ExpressLRS/Handset/Wiki/Filter Boards/20210325_175824414_iOS.jpg

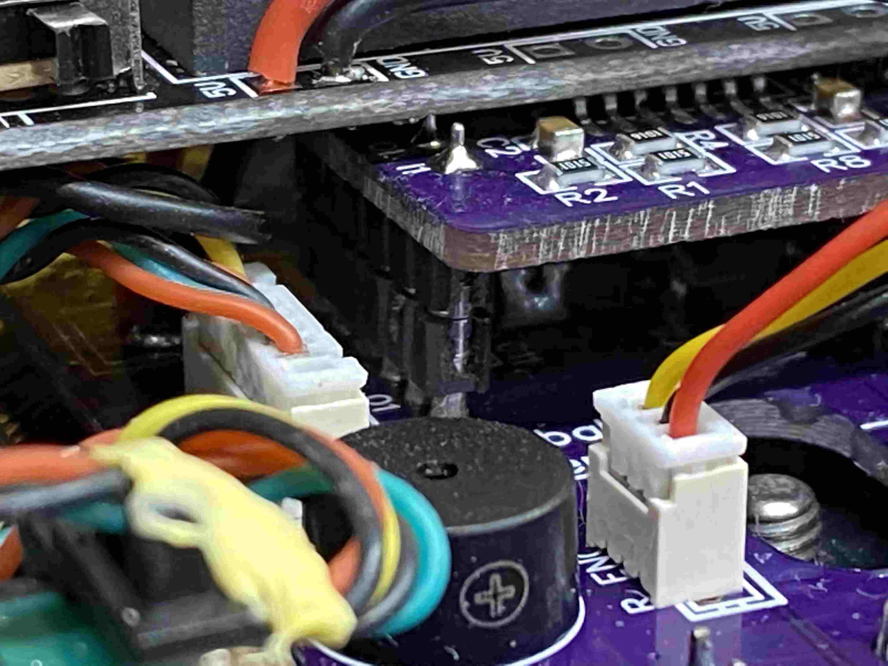
Wiki/Filter Boards/20210325_175824414_iOS.jpg
