ExpressLRS/Handset/Wiki/Filter Boards/20210325_214350122_iOS.jpg

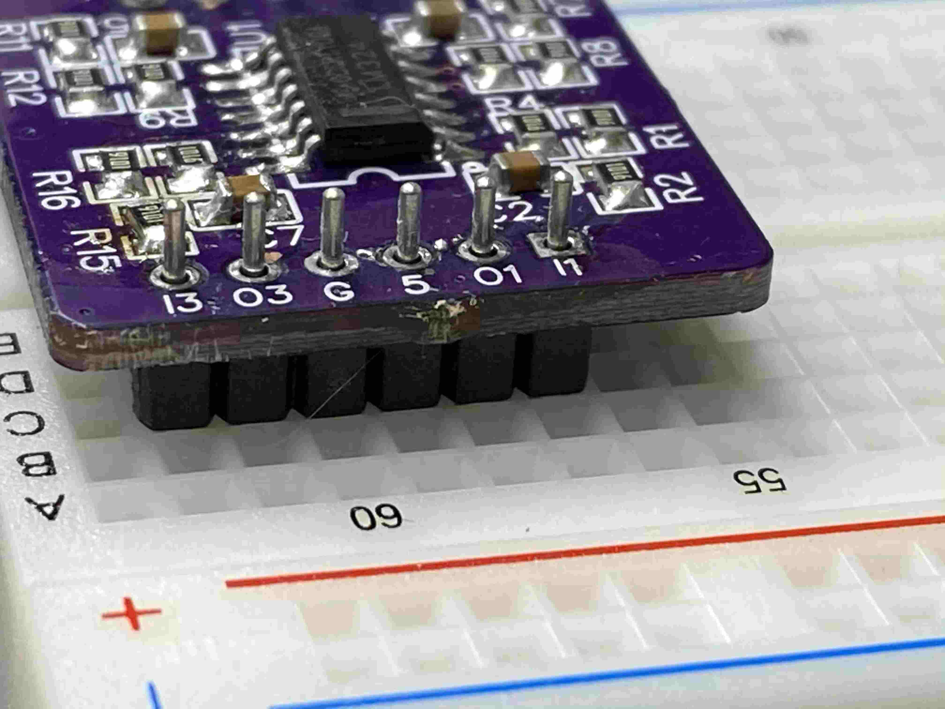
Wiki/Filter Boards/20210325_214350122_iOS.jpg
