ExpressLRS/Handset/Wiki/Filter Boards/20210325_214425201_iOS.jpg

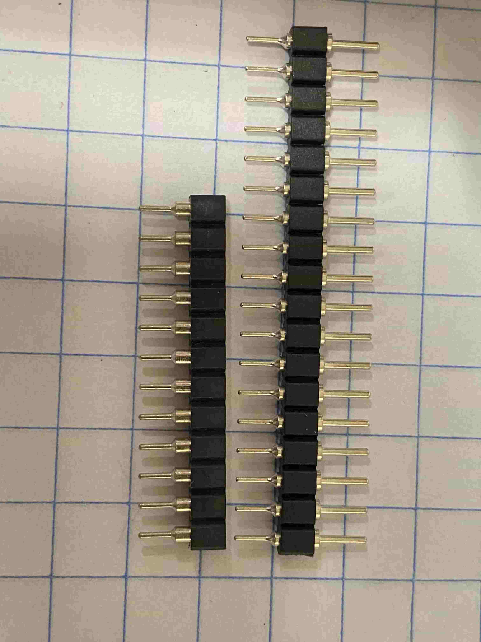
Wiki/Filter Boards/20210325_214425201_iOS.jpg
