ExpressLRS/Handset/Wiki/Filter Boards/20210325_224344439_iOS.jpg

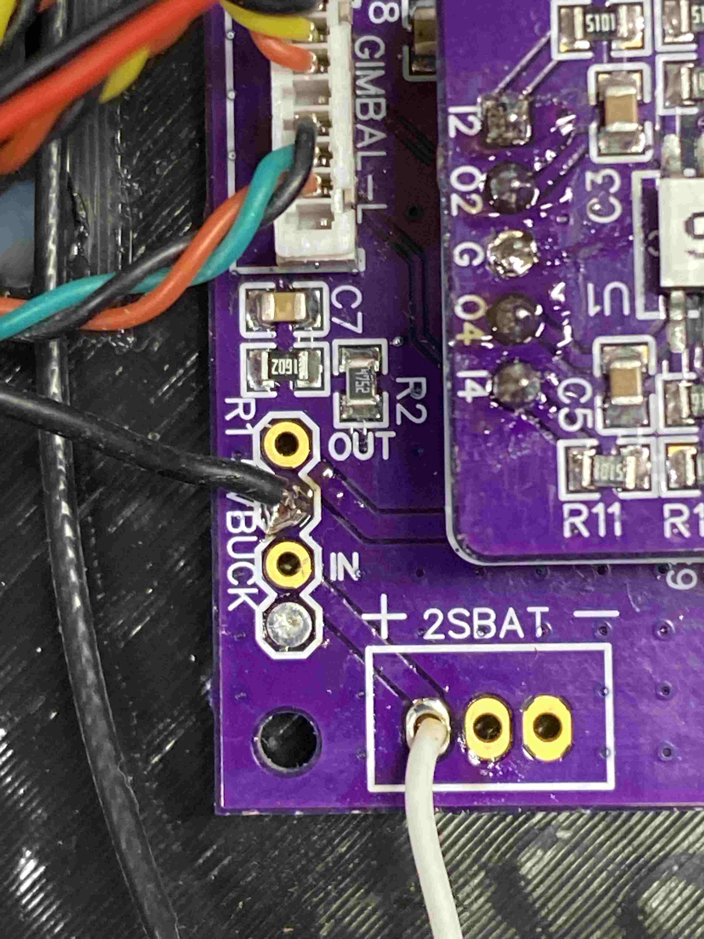
Wiki/Filter Boards/20210325_224344439_iOS.jpg
