ExpressLRS/Handset/Wiki/images/pcbs/filter_top.jpg

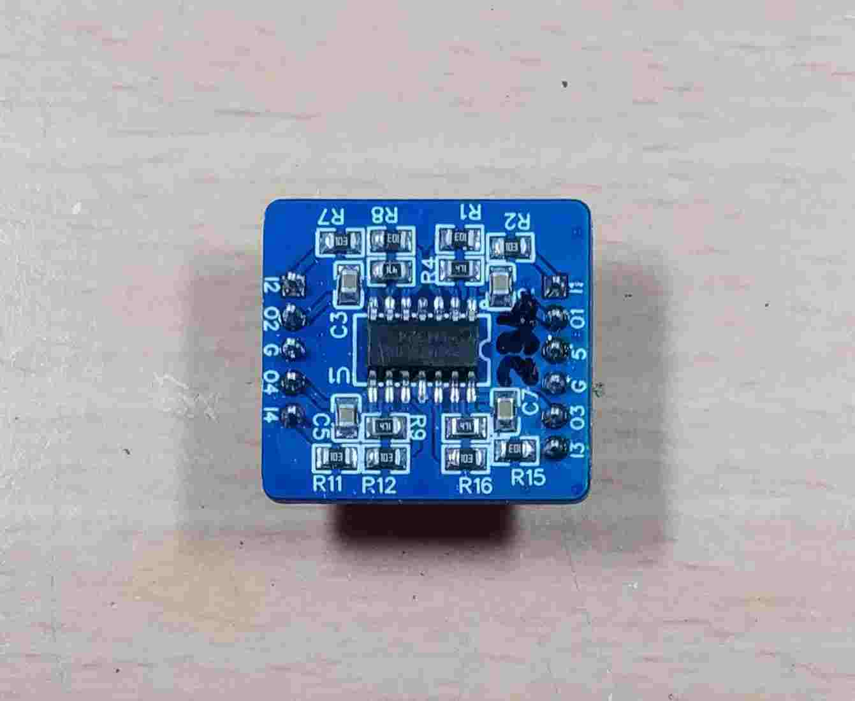
Wiki/images/pcbs/filter_top.jpg
