ExpressLRS/Handset/Wiki/images/pcbs/main_lcd_side.jpg

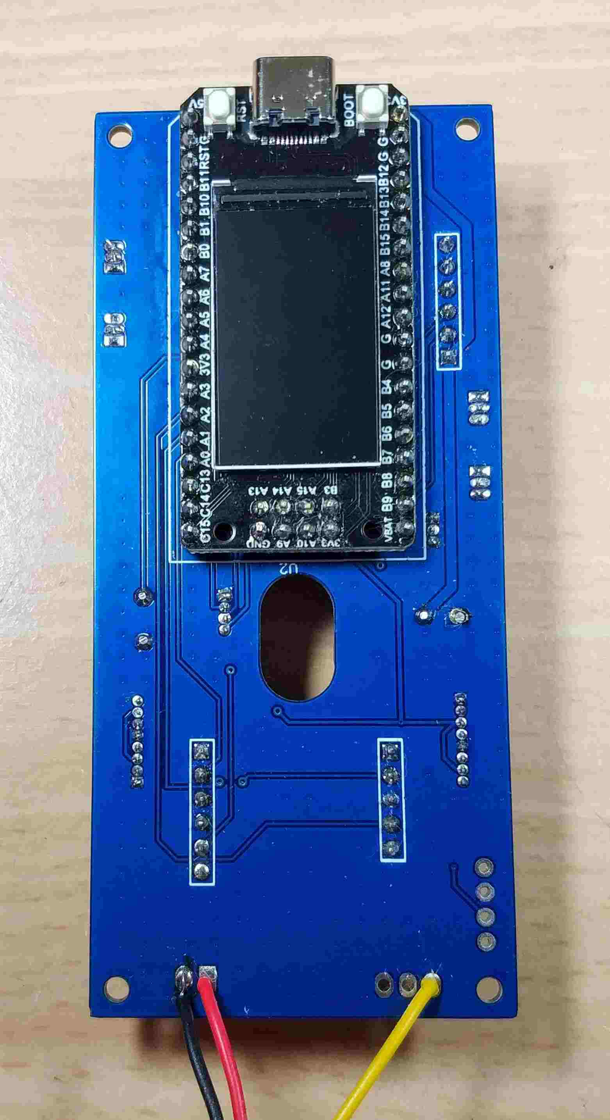
Wiki/images/pcbs/main_lcd_side.jpg
