ExpressLRS/Handset/Wiki/Micro Controller Unit/20210327_000439400_iOS.jpg

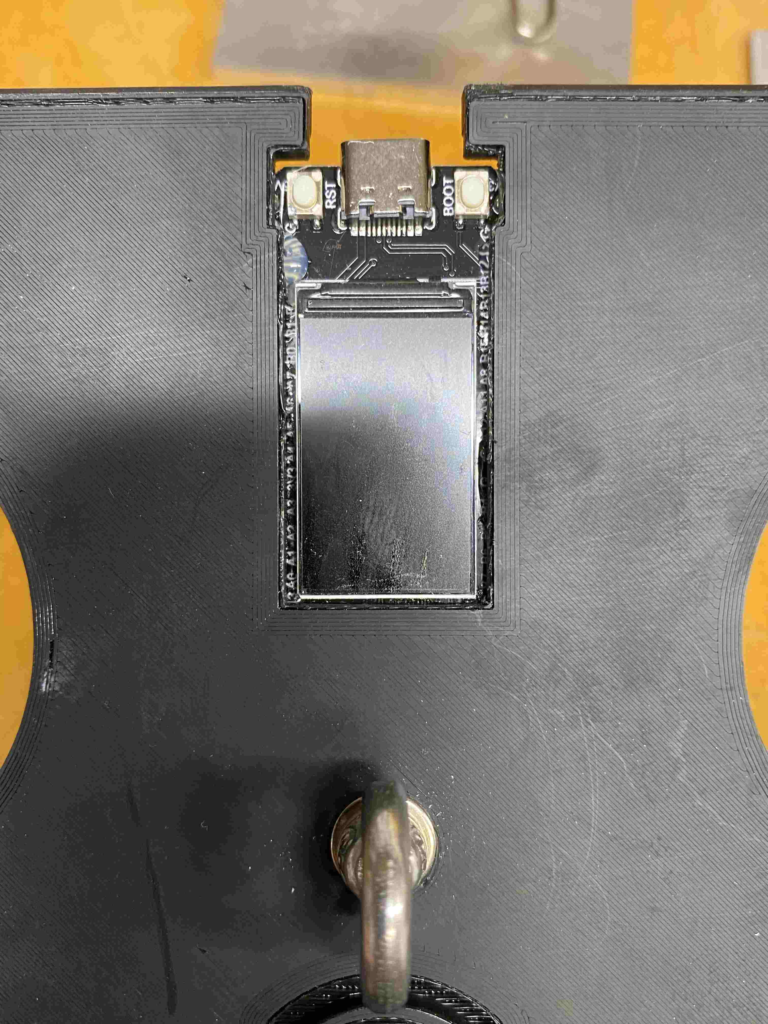
Wiki/Micro Controller Unit/20210327_000439400_iOS.jpg
