ExpressLRS/Handset/Wiki/RF Boards/20210402_183141254_iOS.jpg

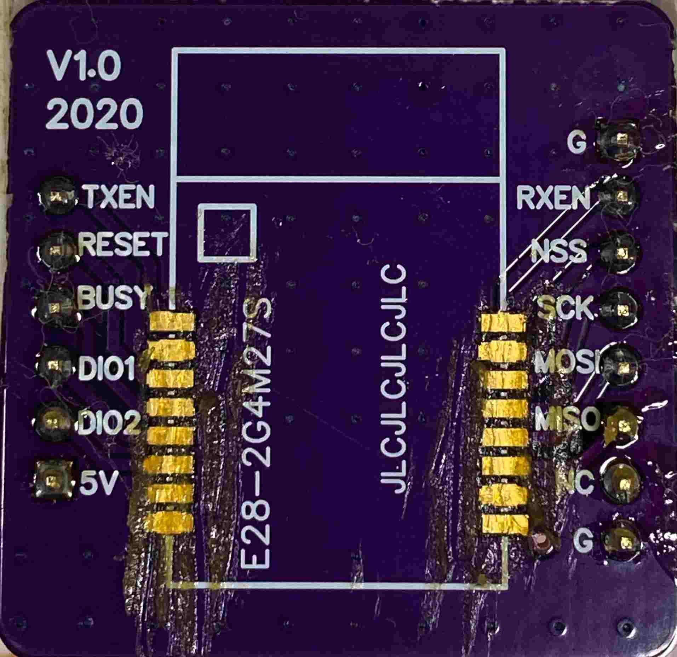
Wiki/RF Boards/20210402_183141254_iOS.jpg
