ExpressLRS/Handset/Wiki/Wireless Charging Cradle/20210328_185023077_iOS.jpg

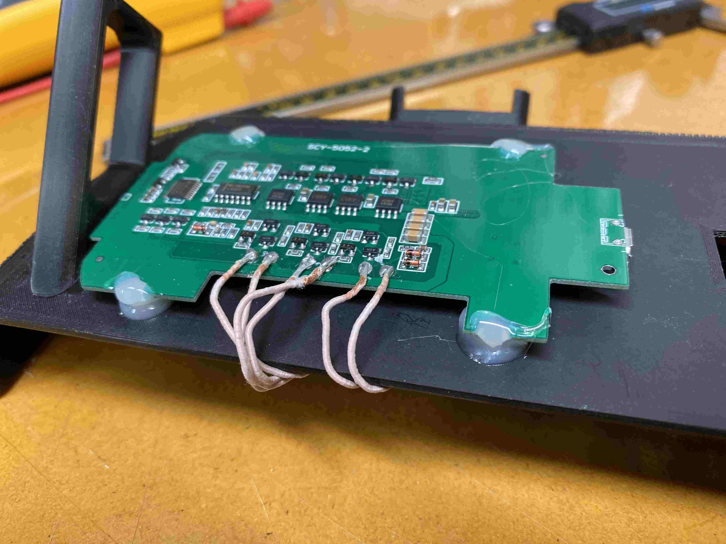
Wiki/Wireless Charging Cradle/20210328_185023077_iOS.jpg
