ExpressLRS/Handset/Wiki/Wireless Charging Cradle/20210328_185138206_iOS.jpg

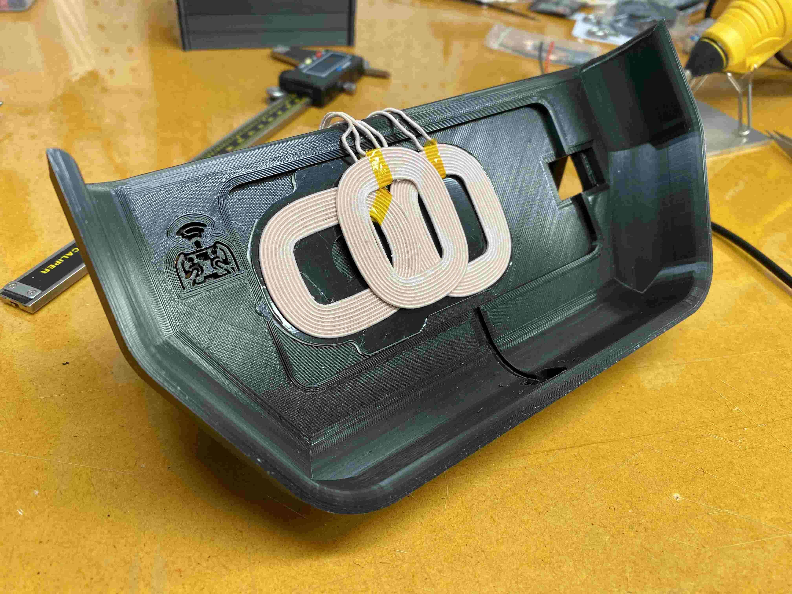
Wiki/Wireless Charging Cradle/20210328_185138206_iOS.jpg
