ExpressLRS/Handset/Wiki/Wireless Charging Cradle/20210328_185158322_iOS.jpg

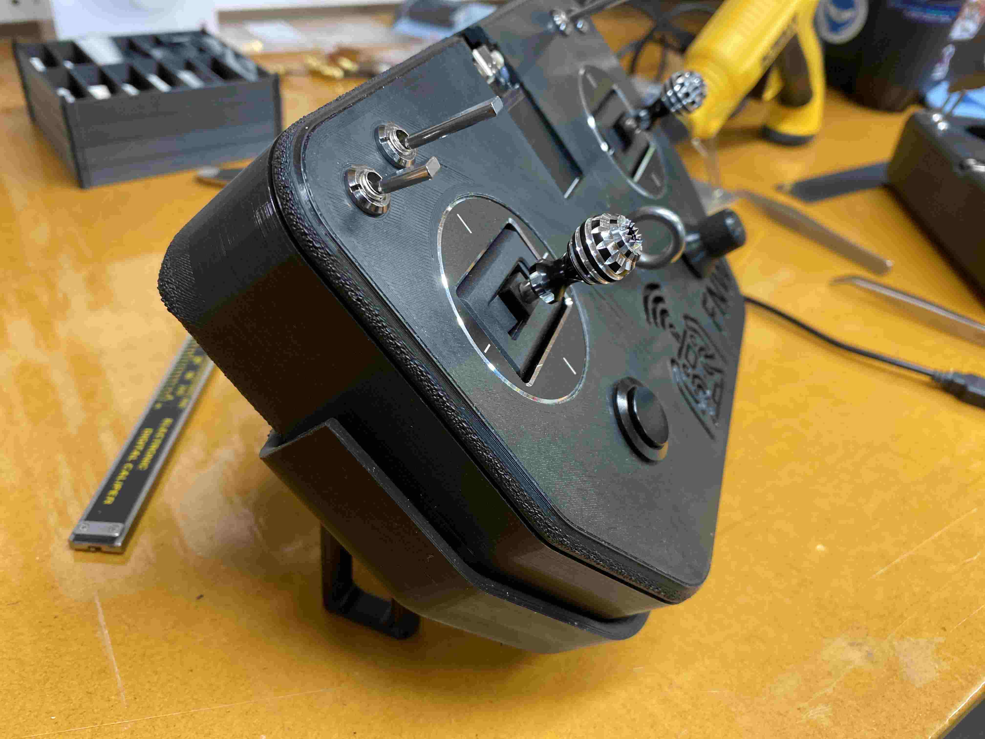
Wiki/Wireless Charging Cradle/20210328_185158322_iOS.jpg
