ExpressLRS/Handset/Wiki/Wireless Charging Cradle/20210328_185213217_iOS.jpg

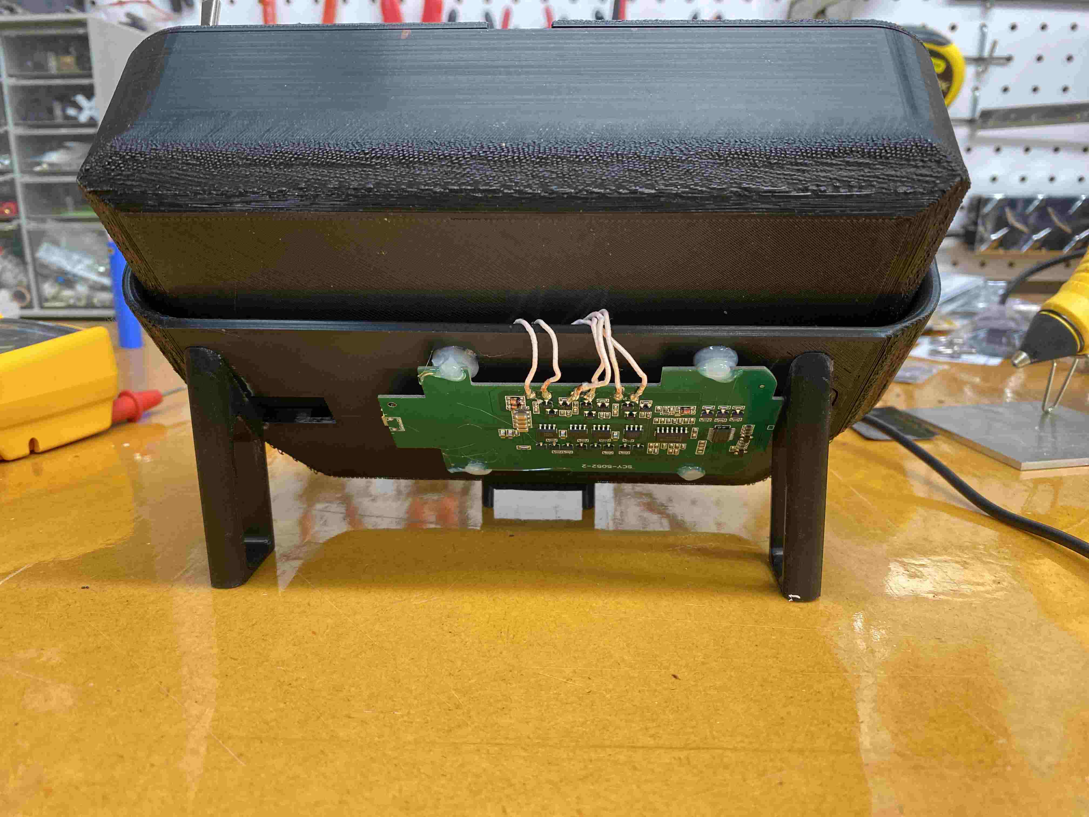
Wiki/Wireless Charging Cradle/20210328_185213217_iOS.jpg
