ExpressLRS/Handset/Wiki/Wireless Charging Cradle/20210328_190506651_iOS.jpg

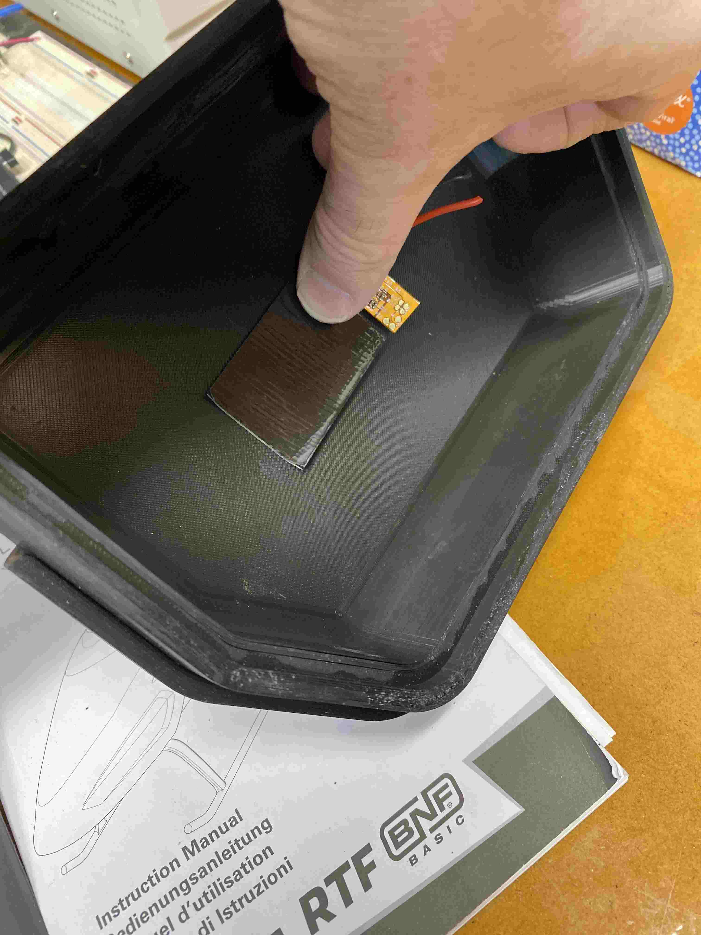
Wiki/Wireless Charging Cradle/20210328_190506651_iOS.jpg
