ExpressLRS/Handset/Wiki/Wireless Charging Cradle/20210410_000010165_iOS.jpg

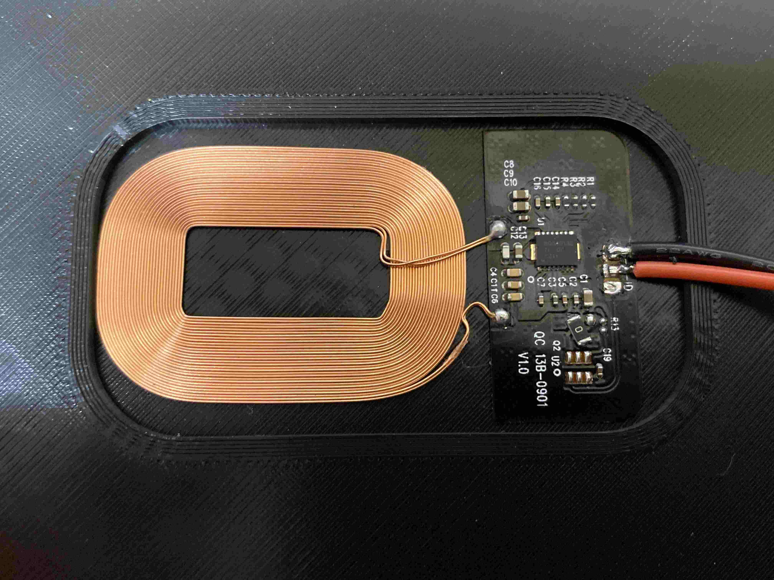
Wiki/Wireless Charging Cradle/20210410_000010165_iOS.jpg
