ExpressLRS/Handset/Wiki/Main Board Assembly/20210325_010320095_iOS.jpg

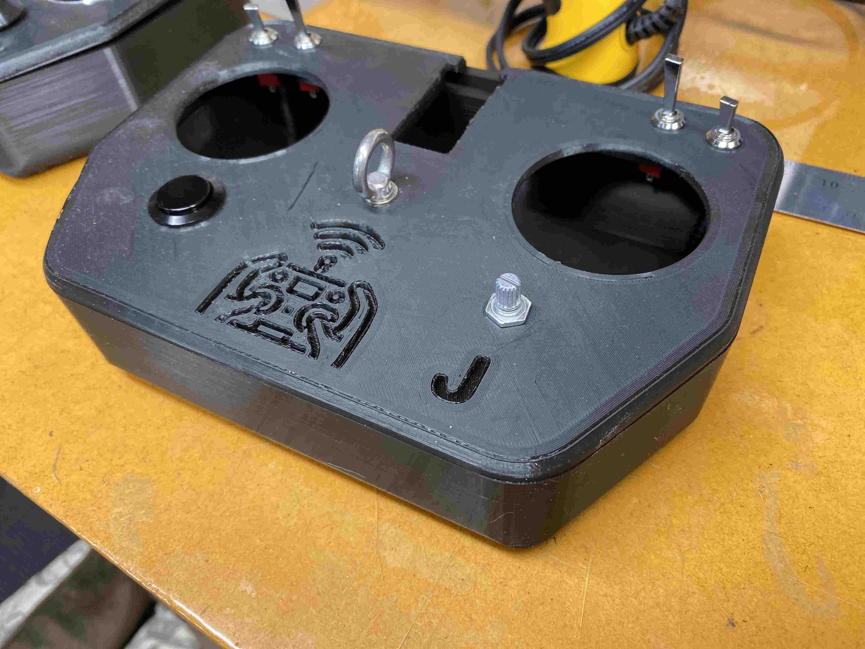
Wiki/Main Board Assembly/20210325_010320095_iOS.jpg
