ExpressLRS/Handset/Wiki/Main Board Assembly/20210327_000455407_iOS.jpg

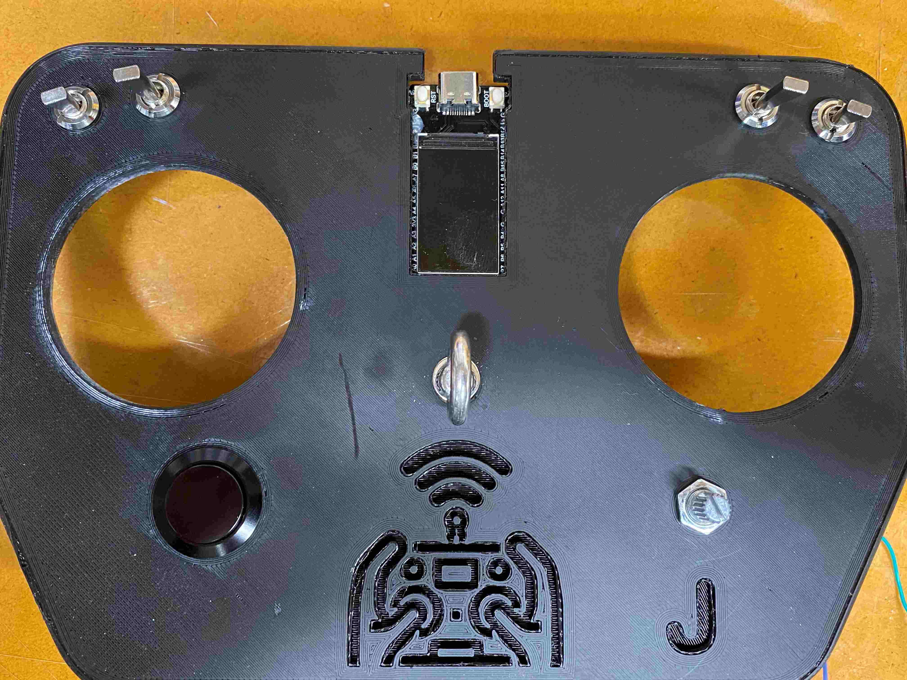
Wiki/Main Board Assembly/20210327_000455407_iOS.jpg
