ExpressLRS/Handset/Wiki/Main Board Assembly/20210327_000602607_iOS.jpg

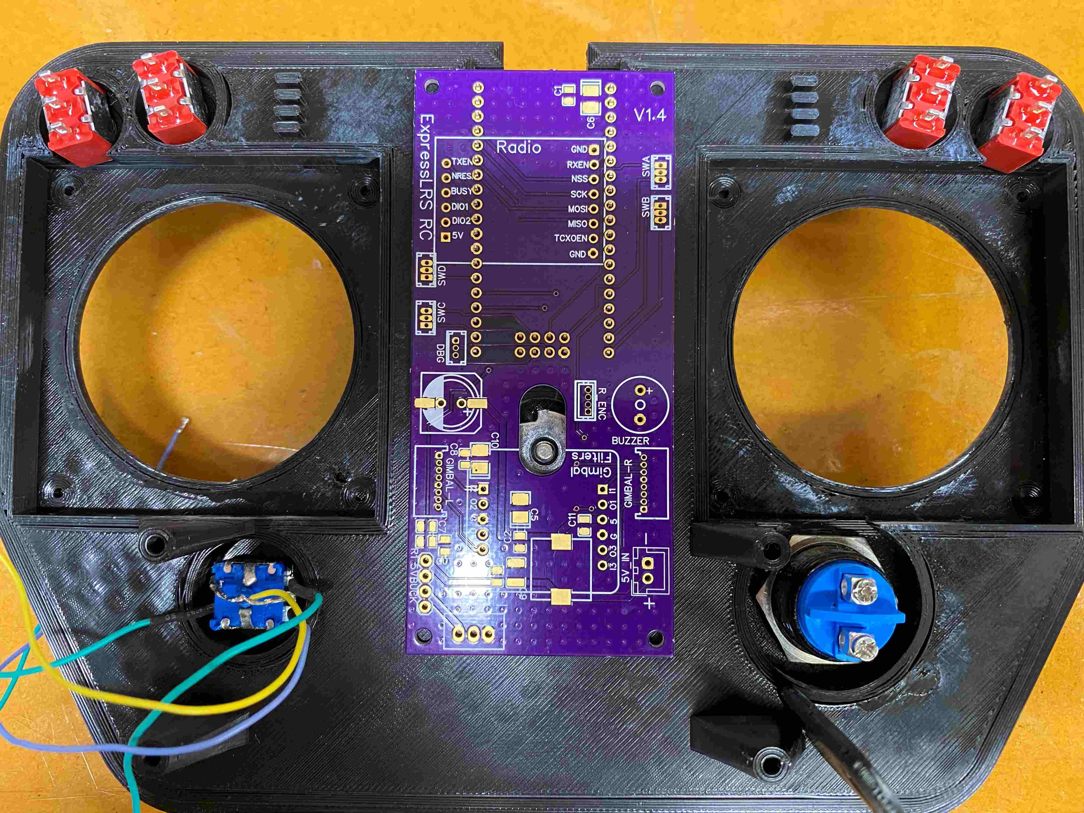
Wiki/Main Board Assembly/20210327_000602607_iOS.jpg
