ExpressLRS/Handset/Wiki/Main Board Assembly/Main PCB.jpg

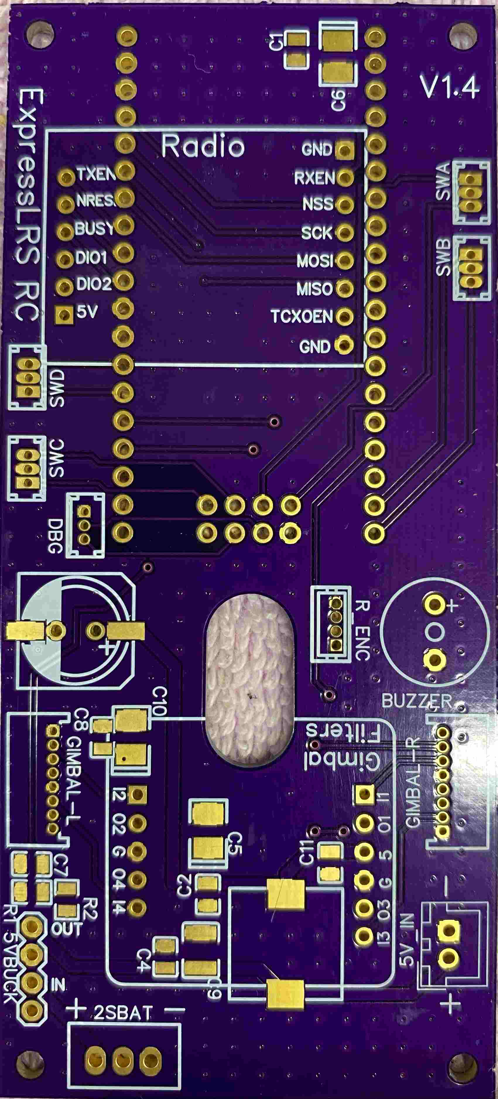
Wiki/Main Board Assembly/Main PCB.jpg
