ExpressLRS/Handset/Wiki/Platform IO Linux Instructions/20210402_213124126_iOS.jpg

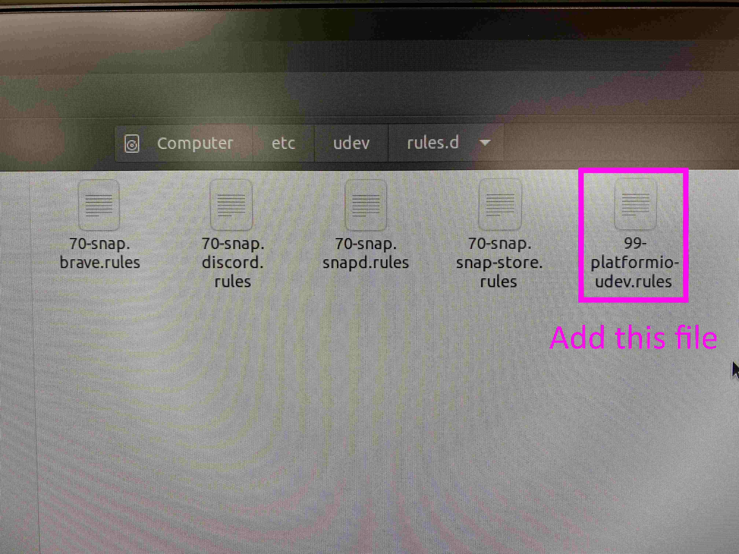
Wiki/Platform IO Linux Instructions/20210402_213124126_iOS.jpg
